KarlVaello/VehicleControlSystem/CCU/Software/CCU/capture/img0.bmp

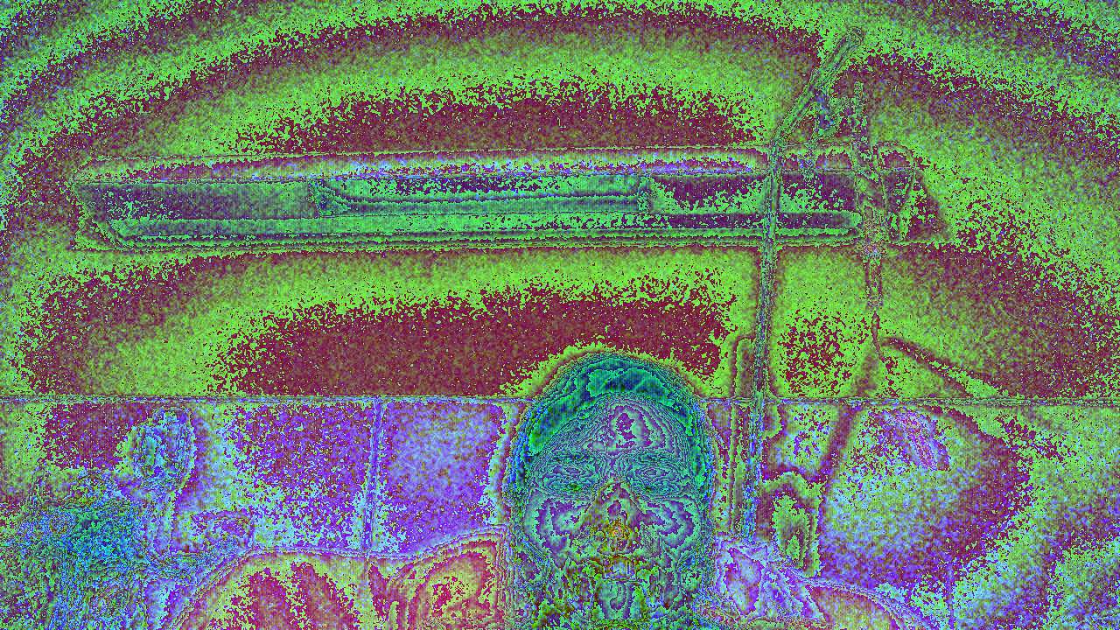
CCU/Software/CCU/capture/img0.bmp
