KarlVaello/VehicleControlSystem/CCU/Software/CCU/capture/img7.bmp

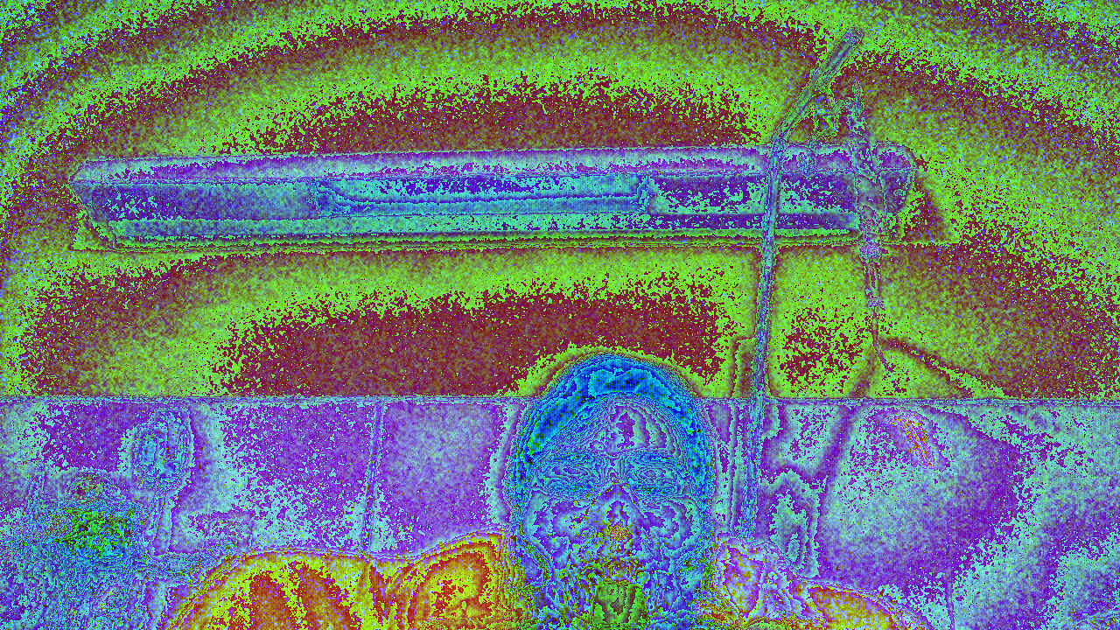
CCU/Software/CCU/capture/img7.bmp
