KarlVaello/VehicleControlSystem/CCU/Software/CCU/capture/img8.bmp

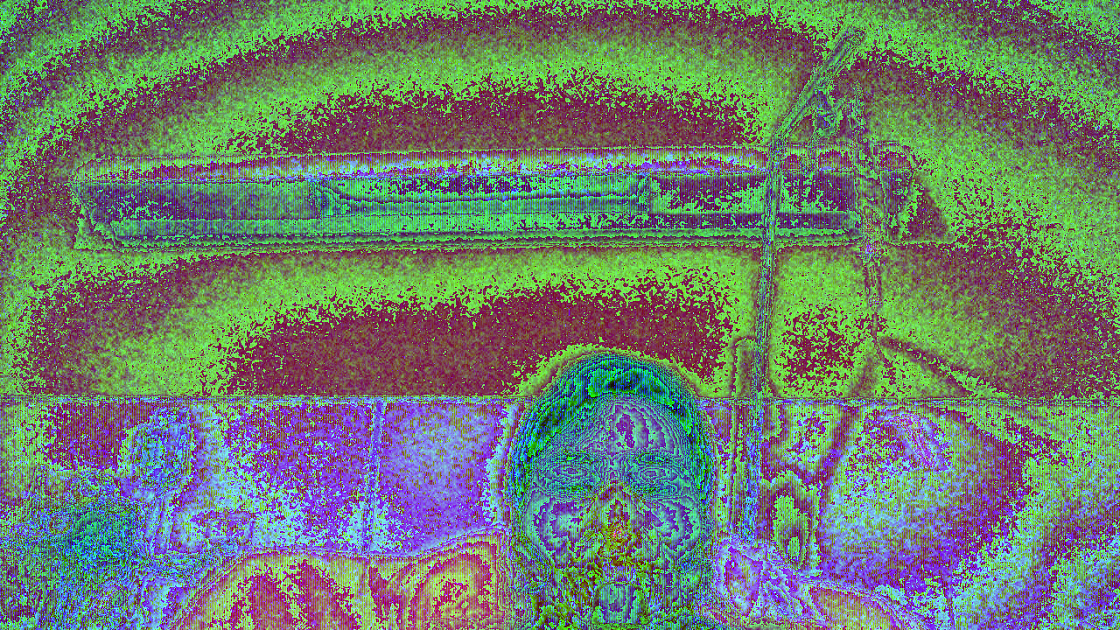
CCU/Software/CCU/capture/img8.bmp
