KarlVaello/VehicleControlSystem/CCU/Software/CCU/capture/img9.bmp

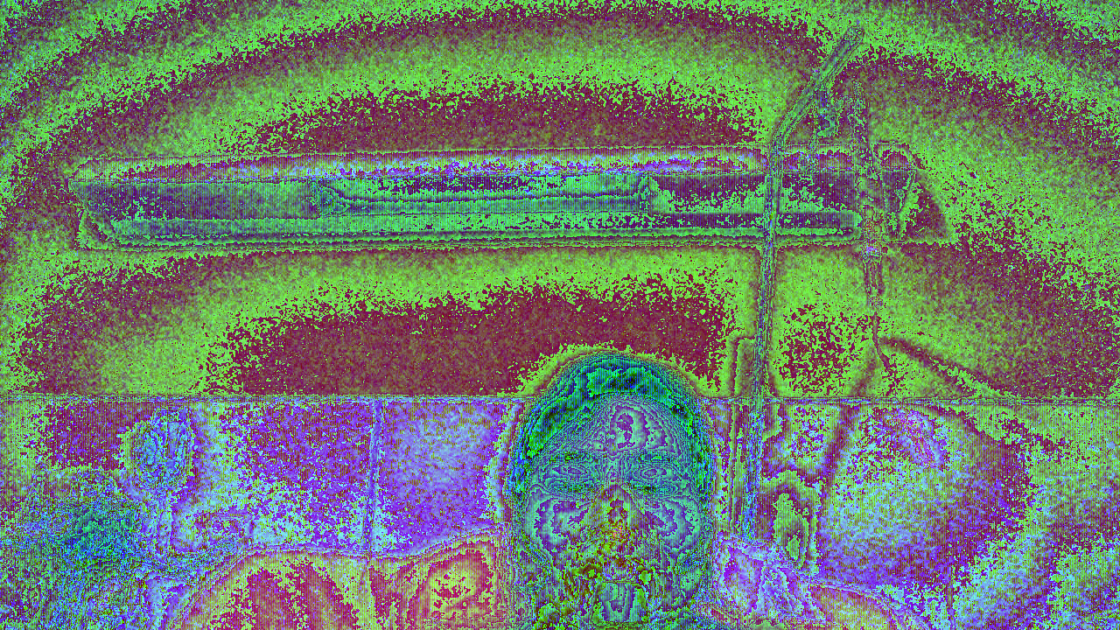
CCU/Software/CCU/capture/img9.bmp
