KarlVaello/VehicleControlSystem/CCU/Software/CCU/capture/img11.bmp

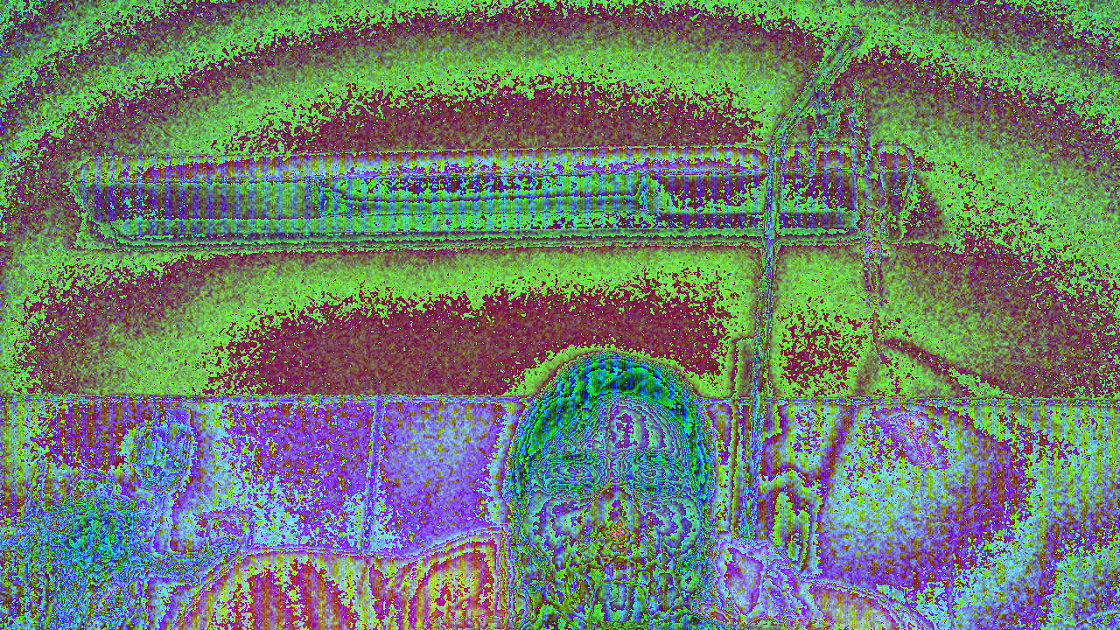
CCU/Software/CCU/capture/img11.bmp
