KarlVaello/VehicleControlSystem/CCU/Software/CCU/capture/img14.bmp

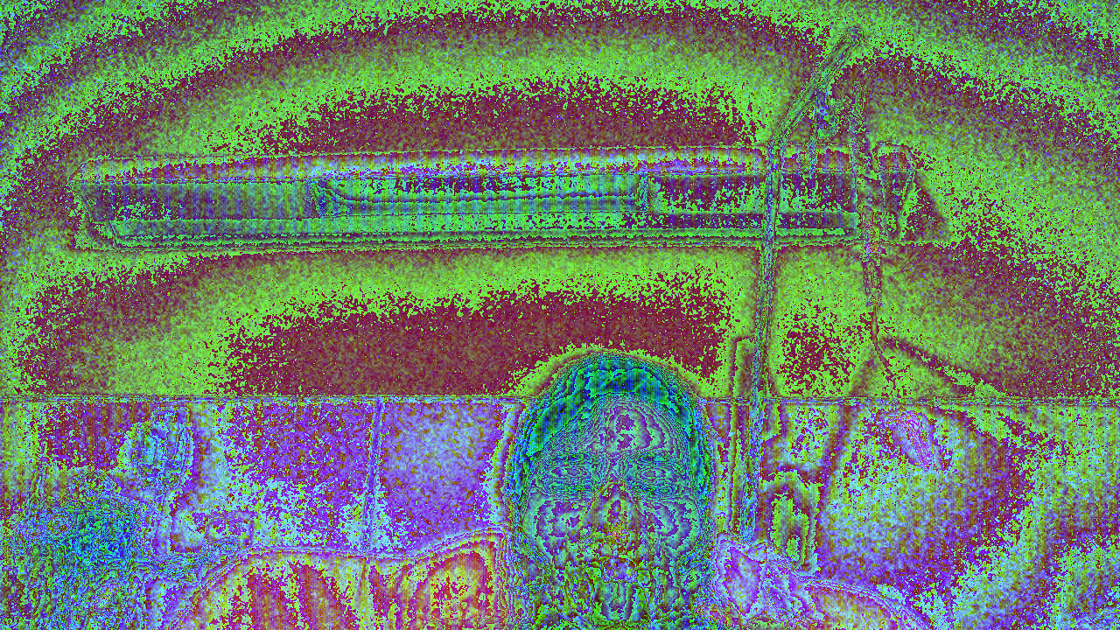
CCU/Software/CCU/capture/img14.bmp
