KarlVaello/VehicleControlSystem/CCU/Software/CCU/capture/img19.bmp

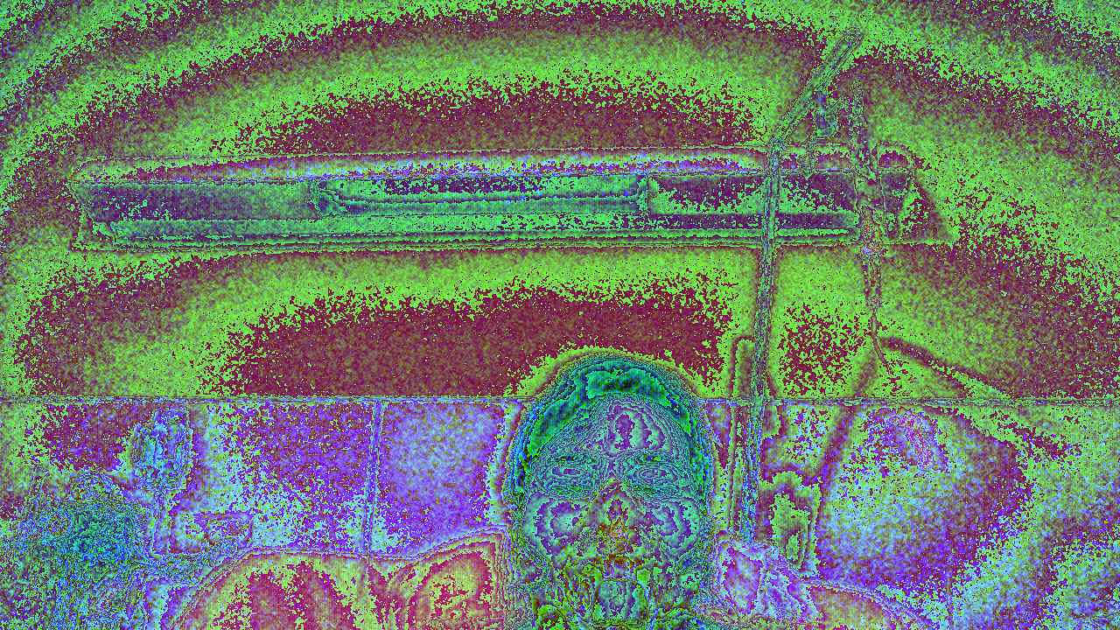
CCU/Software/CCU/capture/img19.bmp
