KarlVaello/VehicleControlSystem/CCU/Software/CCU/capture/img21.bmp

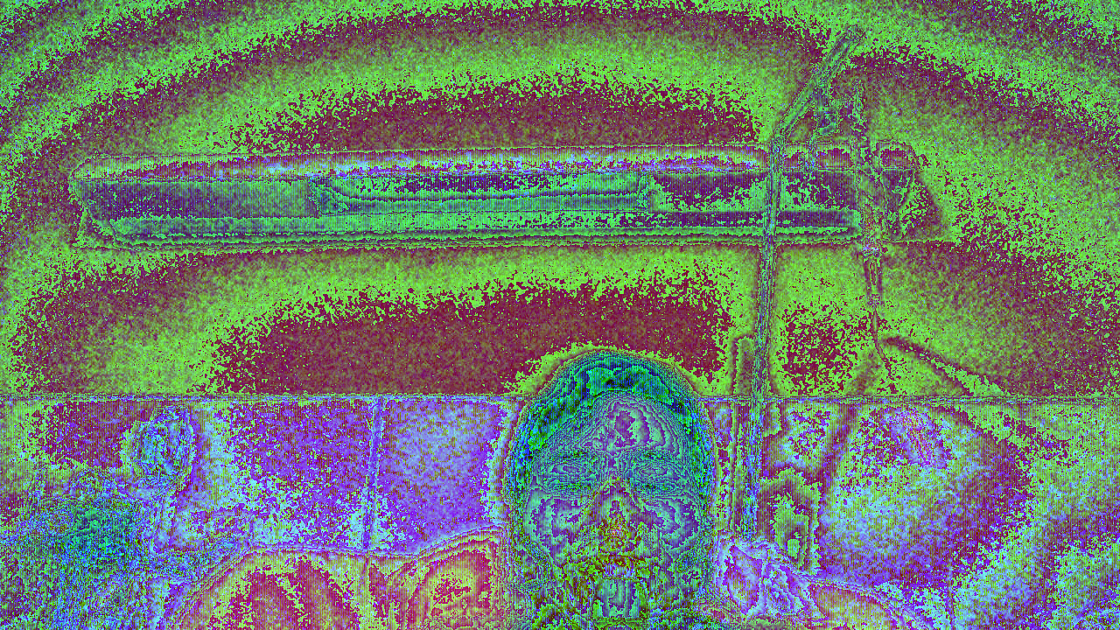
CCU/Software/CCU/capture/img21.bmp
