KarlVaello/VehicleControlSystem/CCU/Software/CCU/capture/img22.bmp

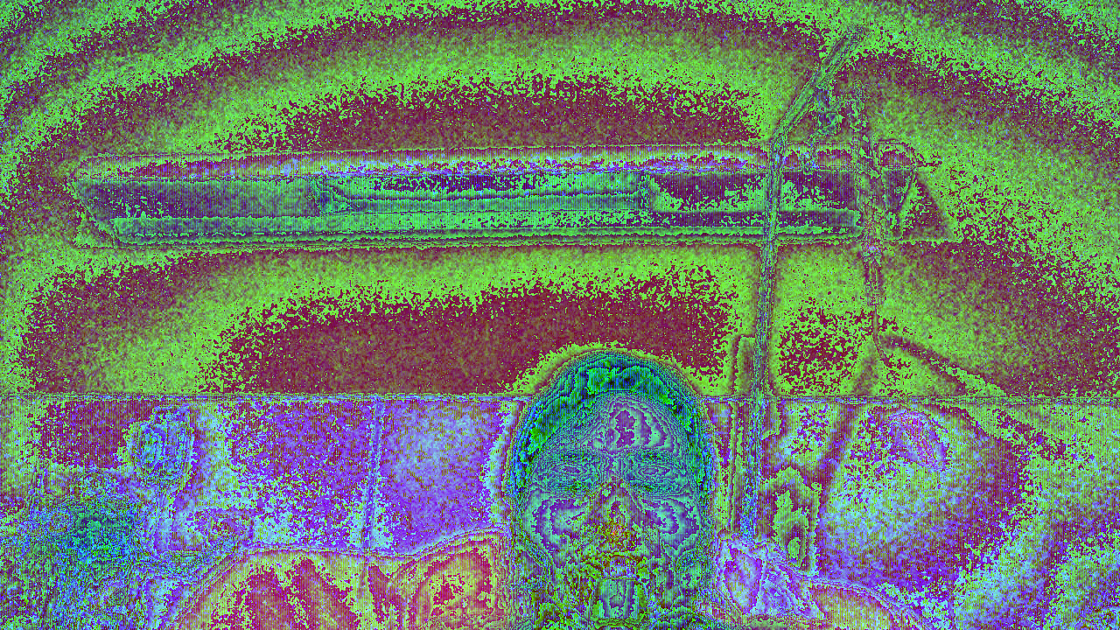
CCU/Software/CCU/capture/img22.bmp
