KarlVaello/VehicleControlSystem/CCU/Software/CCU/capture/img23.bmp

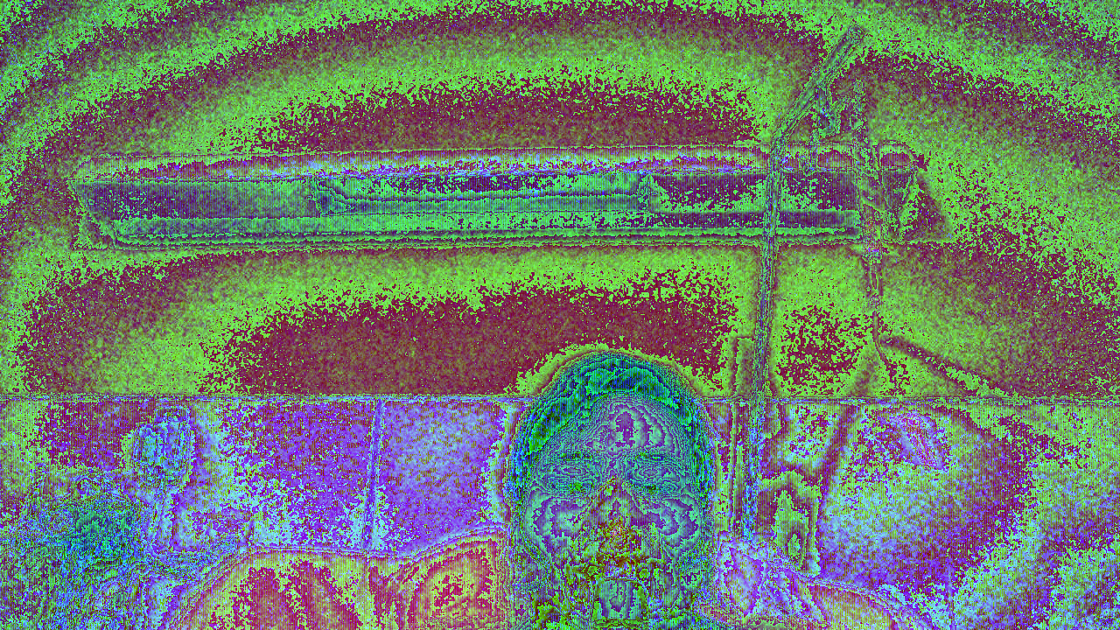
CCU/Software/CCU/capture/img23.bmp
