KarlVaello/VehicleControlSystem/CCU/Software/CCU/capture/img25.bmp

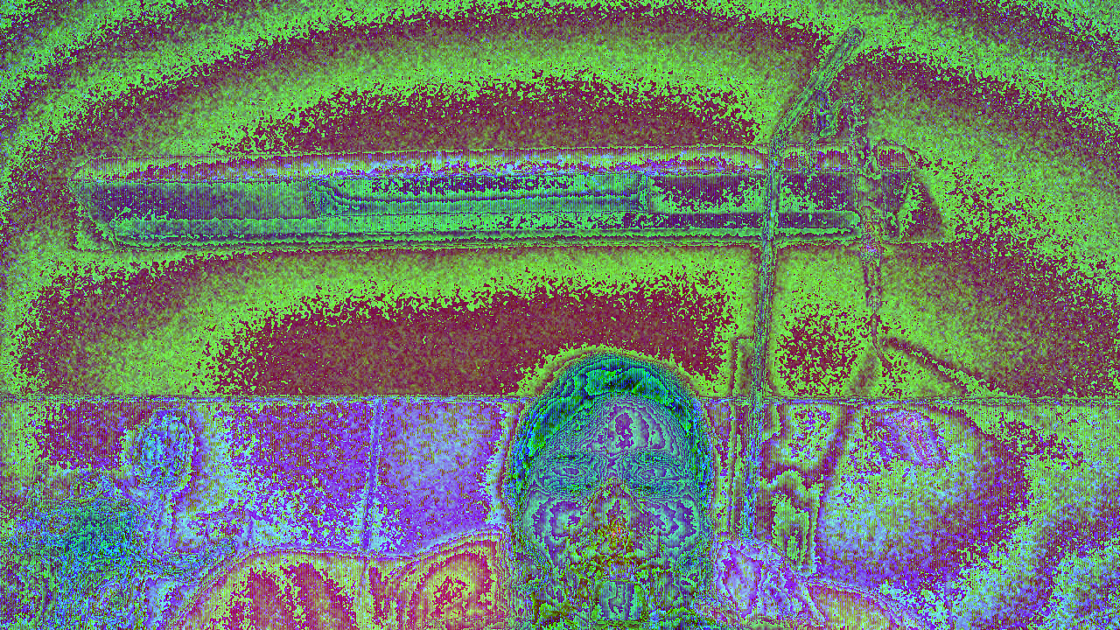
CCU/Software/CCU/capture/img25.bmp
