KarlVaello/VehicleControlSystem/CCU/Software/CCU/capture/img37.bmp

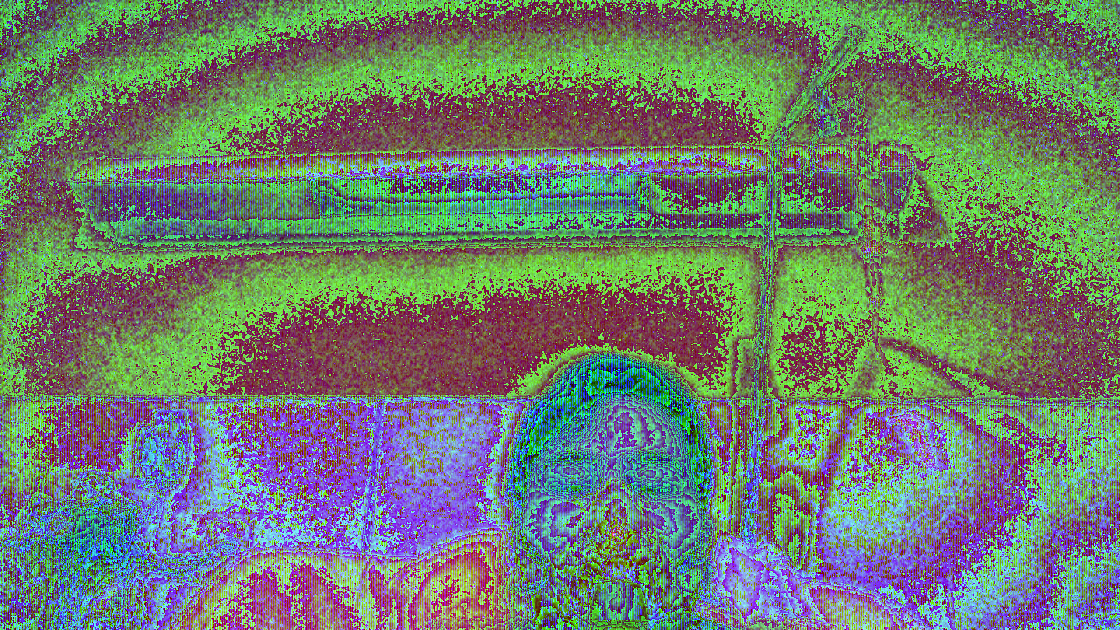
CCU/Software/CCU/capture/img37.bmp
