KarlVaello/VehicleControlSystem/CCU/Software/CCU/capture/img41.bmp

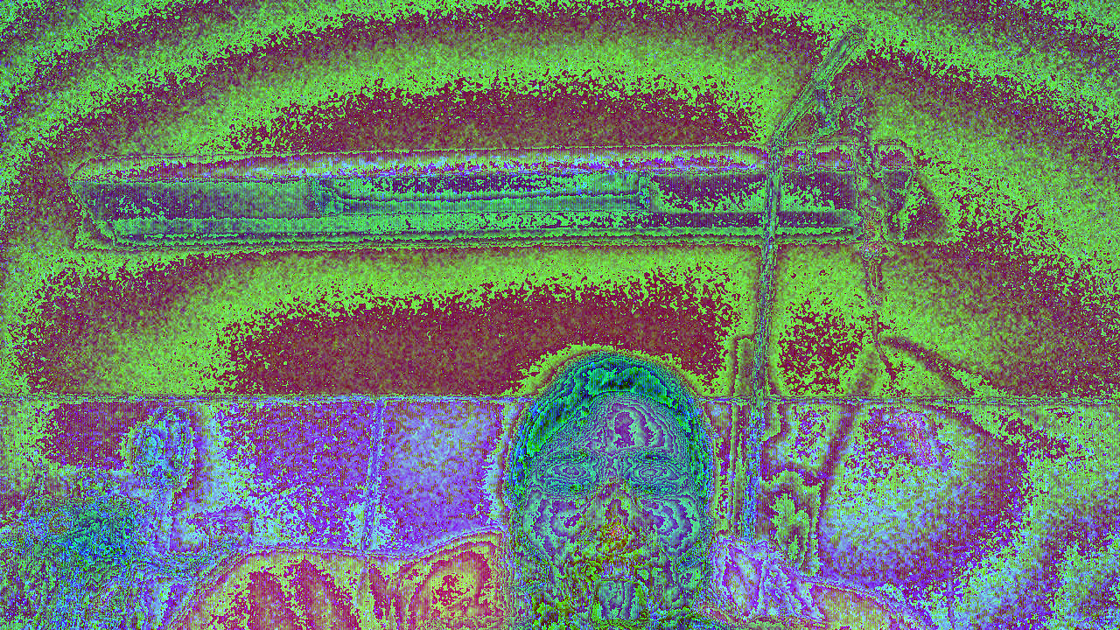
CCU/Software/CCU/capture/img41.bmp
