KarlVaello/VehicleControlSystem/CCU/Software/CCU/capture/img46.bmp

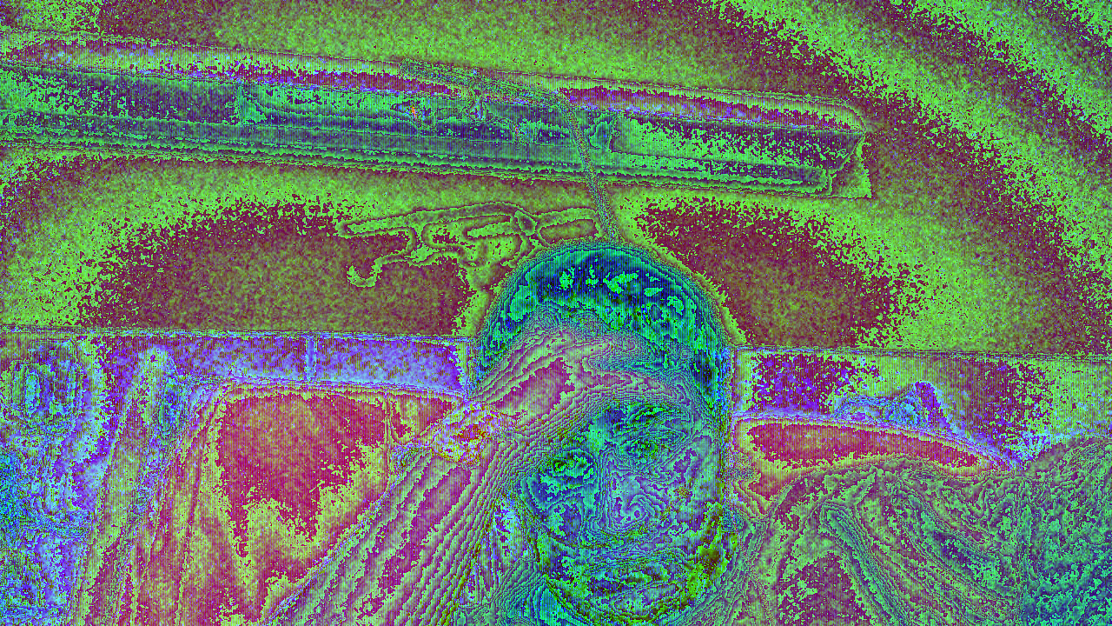
CCU/Software/CCU/capture/img46.bmp
