KarlVaello/VehicleControlSystem/CCU/Software/CCU/capture/img47.bmp

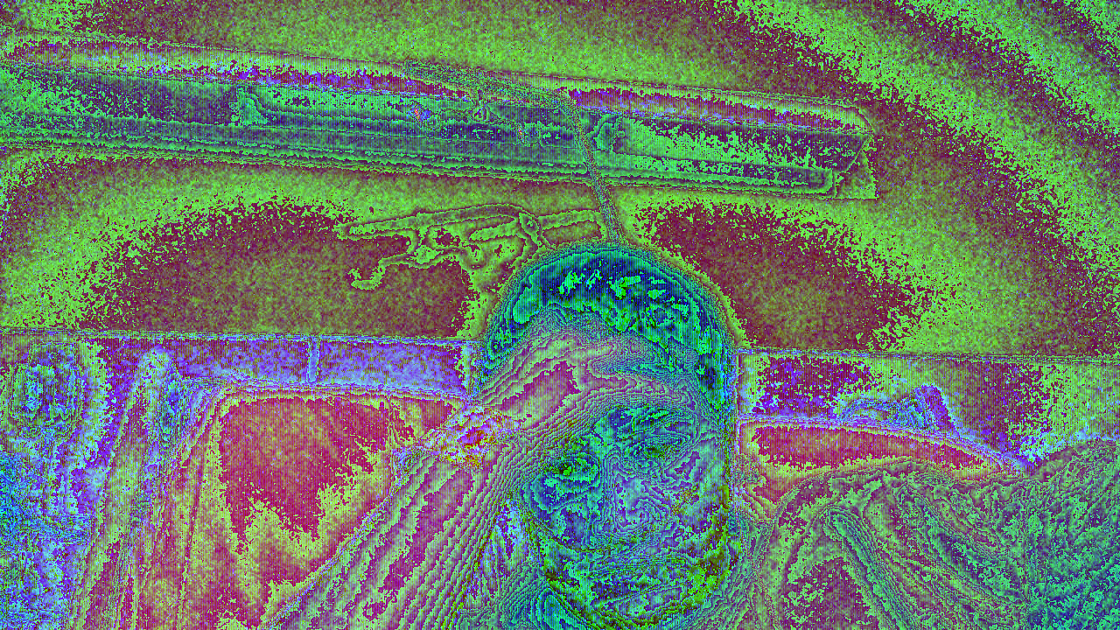
CCU/Software/CCU/capture/img47.bmp
