KarlVaello/VehicleControlSystem/CCU/Software/CCU/capture/img48.bmp

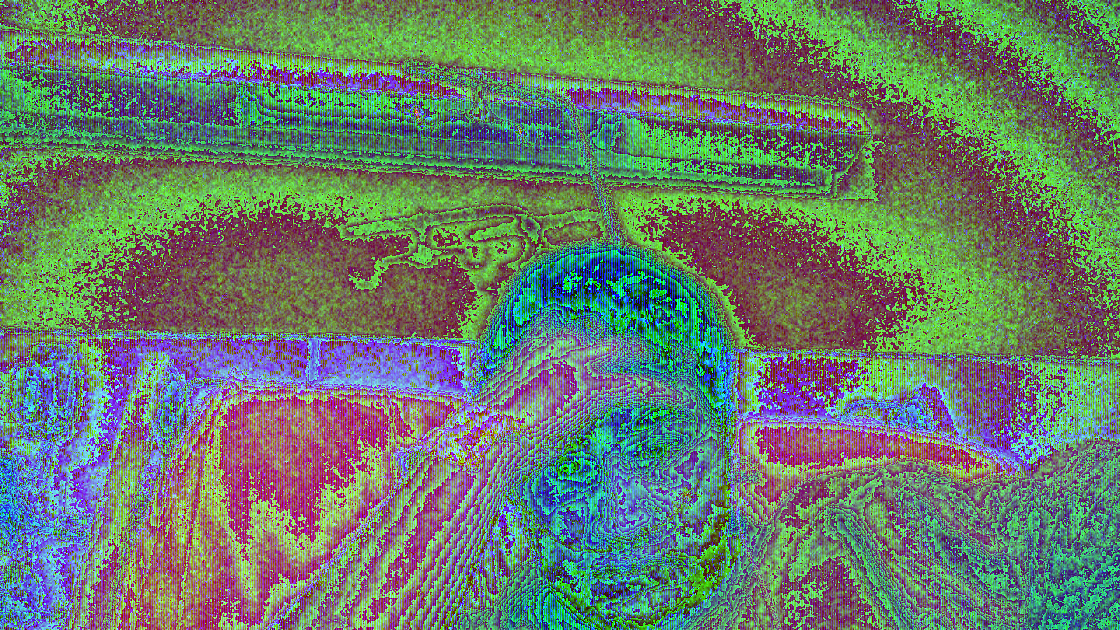
CCU/Software/CCU/capture/img48.bmp
